echox/weberknecht0.5/parts/openscad/clip.scad

difference() {
    cube([8.5,7,7]);
    translate([2,0,2]) cube([4.5,7,7]);
}
